IHot98/active-bass/KiCad-PCB/Slike/20210929_140951.jpg

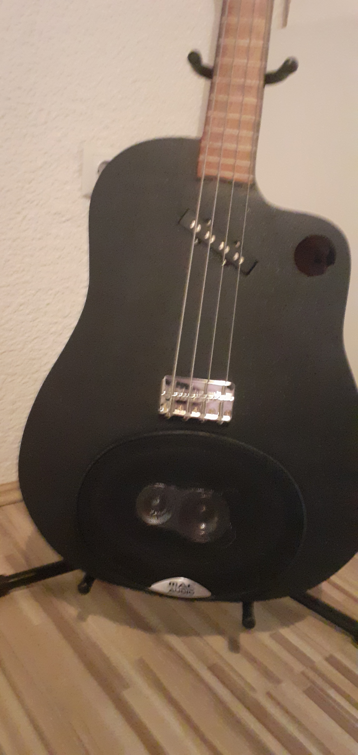
KiCad-PCB/Slike/20210929_140951.jpg
